Wireb/Cyphercon-5_3-2022/inkscape/coyote/coyote-F_SilkS_connect2.png

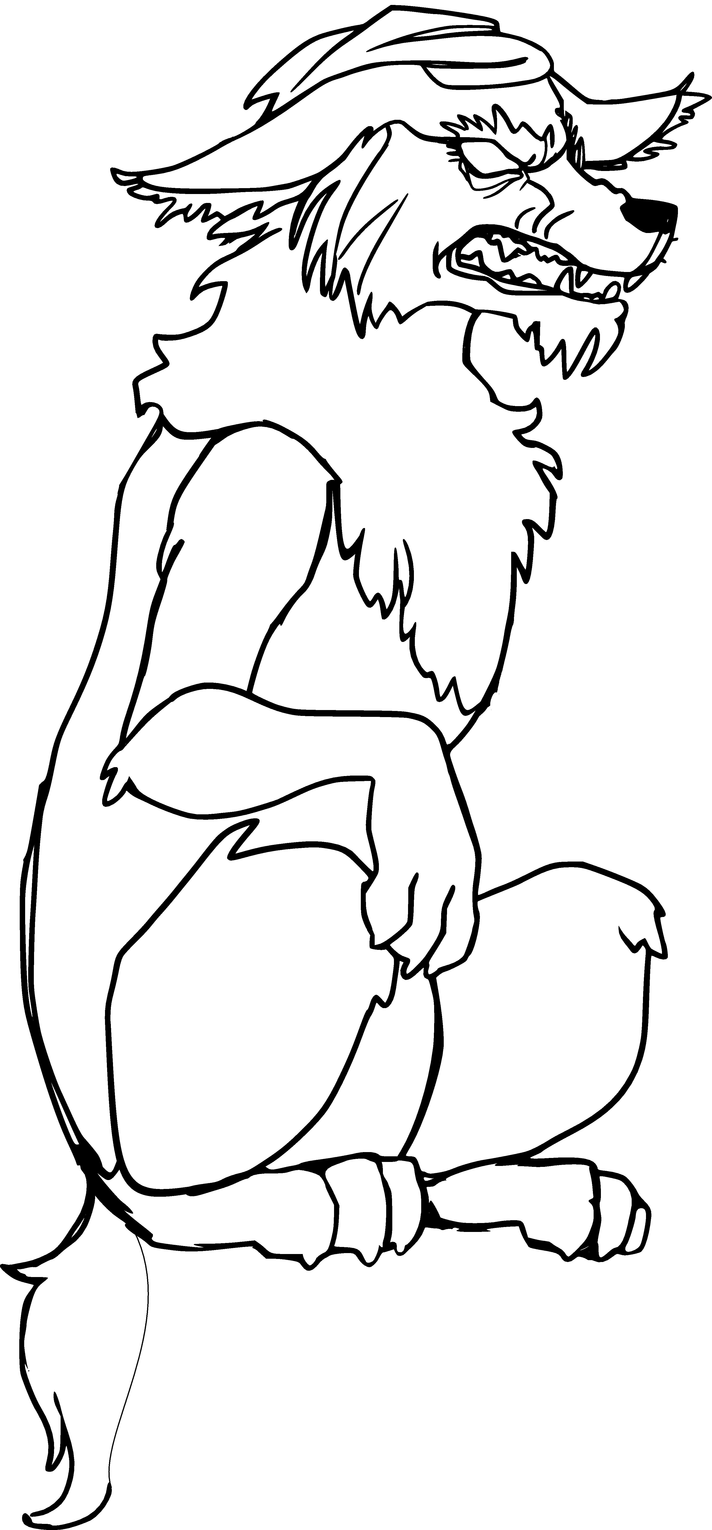
inkscape/coyote/coyote-F_SilkS_connect2.png
