Wireb/Cyphercon-5_3-2022/inkscape/Flamingo/2_tone_temp-F_SilkS_cleaned_thick.png

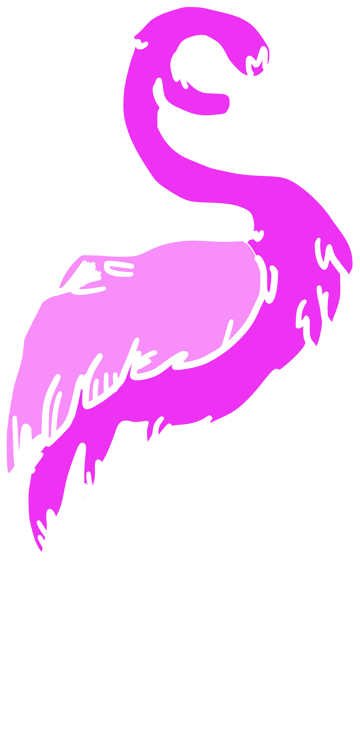
inkscape/Flamingo/2_tone_temp-F_SilkS_cleaned_thick.png
