Wireb/Cyphercon-5_3-2022/inkscape/Llama/llama-F_SilkS_hair.png

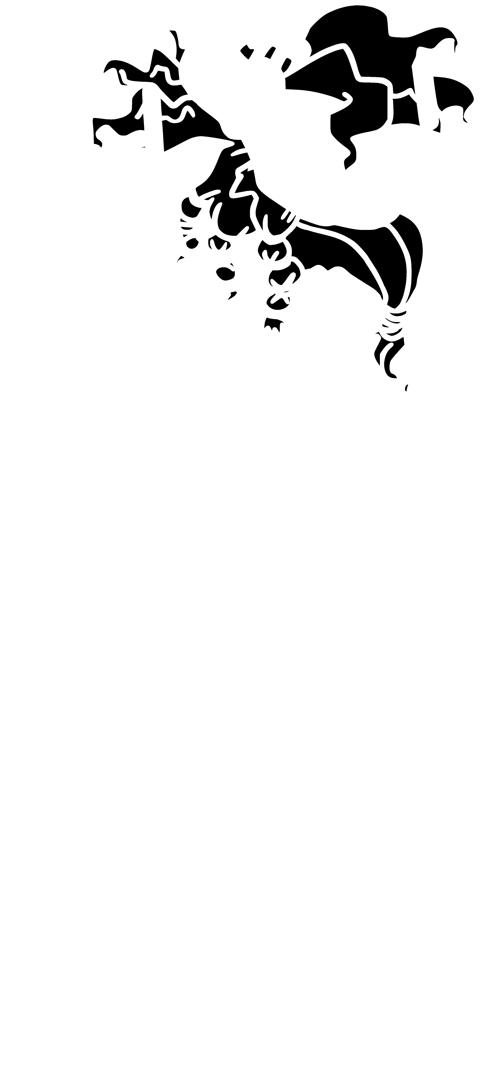
inkscape/Llama/llama-F_SilkS_hair.png
