Wireb/Cyphercon-5_3-2022/inkscape/Parrot/Parrot-F_SilkS.png

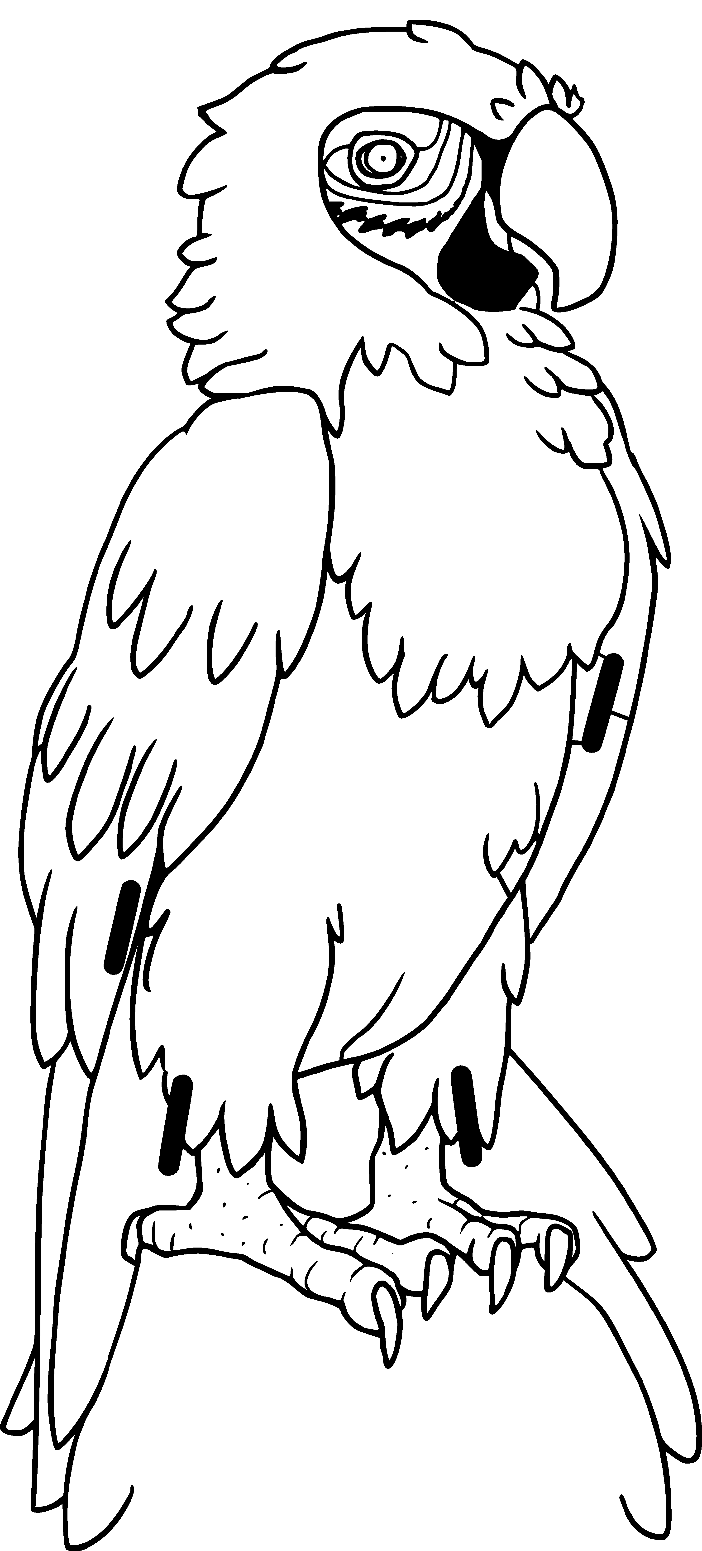
inkscape/Parrot/Parrot-F_SilkS.png
