Wireb/Cyphercon-5_3-2022/inkscape/Parrot/Parrot-F_SilkS_outline_inv.png

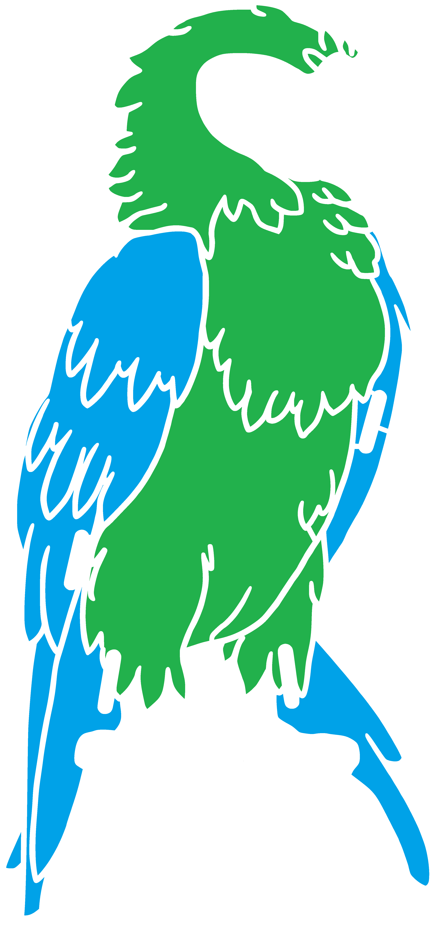
inkscape/Parrot/Parrot-F_SilkS_outline_inv.png
