Wireb/Cyphercon-5_3-2022/FreeCAD/tymkrs_Cyphercon_2020/wash_holder_base.stl

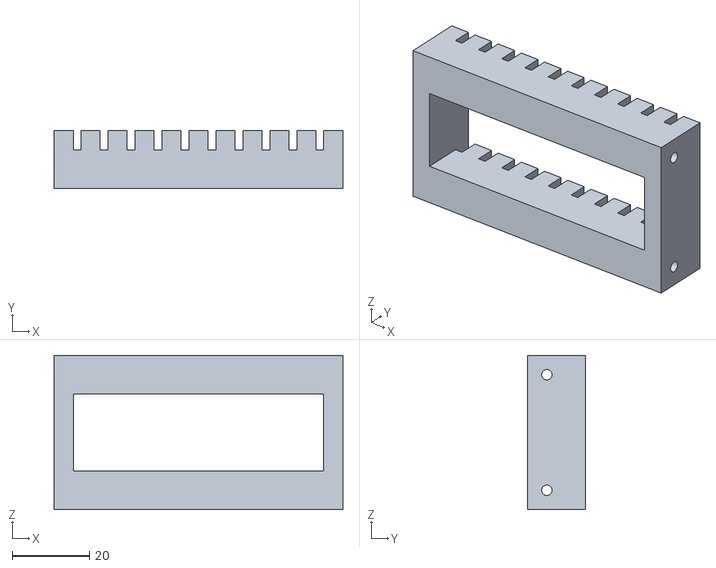
[picture p23: CAD file, 2022-05-03]
FreeCAD/tymkrs_Cyphercon_2020/wash_holder_base.stl
75.0 x 15.0 x 40.0
