Wireb/Cyphercon-5_3-2022/FreeCAD/Start button-2022/iris_arm (Meshed)001.stl

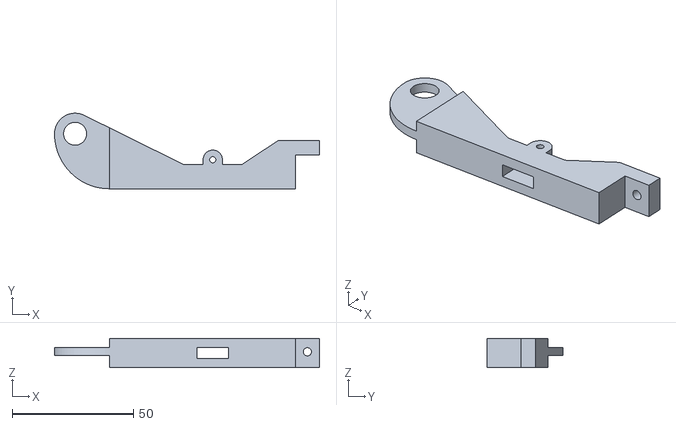
[picture p24: CAD file, 2022-05-03]
FreeCAD/Start button-2022/iris_arm (Meshed)001.stl
109.5 x 31.2 x 12.0
