Wireb/Cyphercon-5_3-2022/FreeCAD/tymkrs_Cyphercon_2020/bottle_button_support.FCStd

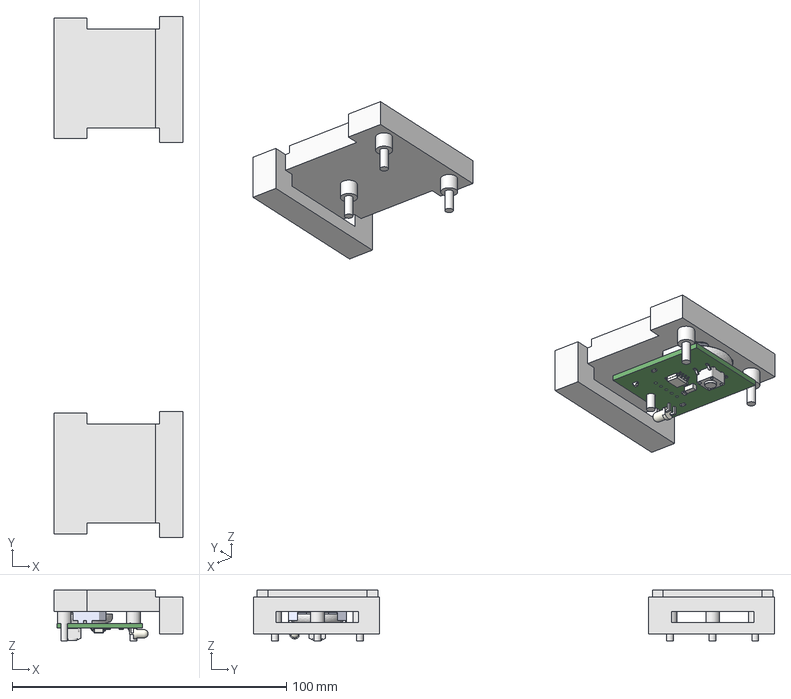
[picture p25: CAD file, 2022-05-03]
FreeCAD/tymkrs_Cyphercon_2020/bottle_button_support.FCStd
47.0 x 190.0 x 18.5 mm
button_carrier
button_carrier (Meshed)
