Wireb/Cyphercon-5_3-2022/FreeCAD/Start button-2022/1185 Massive Arcade Button 100mm.step

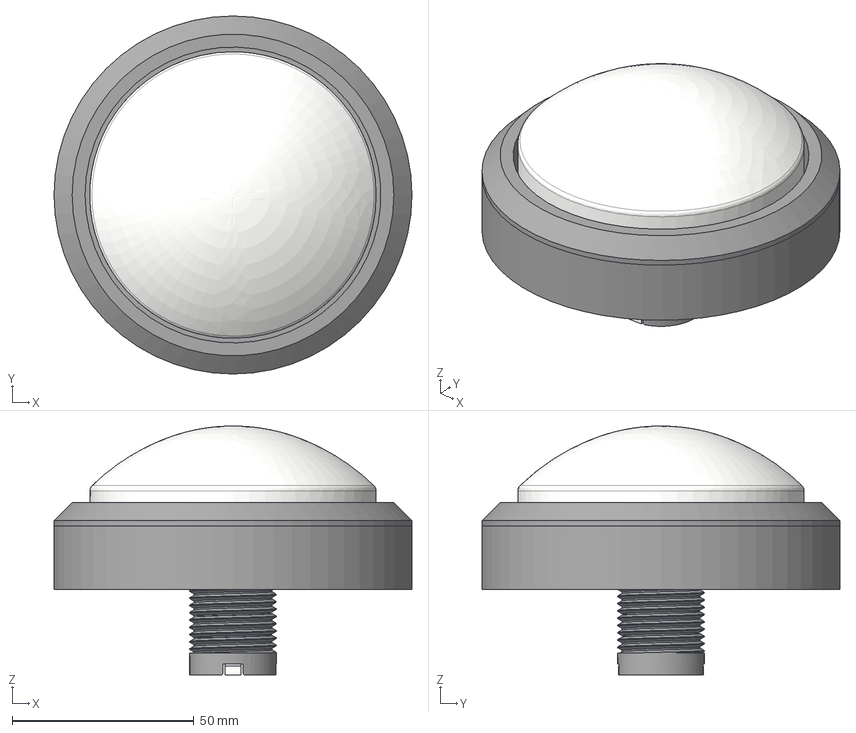
[picture p26: CAD file, 2022-05-03]
FreeCAD/Start button-2022/1185 Massive Arcade Button 100mm.step
98.5 x 98.5 x 68.5 mm
Base
Holder
Actuator
Spring
Dome
