Wireb/Cyphercon-5_3-2022/FreeCAD/tymkrs_Cyphercon_2020/Llama_top_flock (Meshed).stl

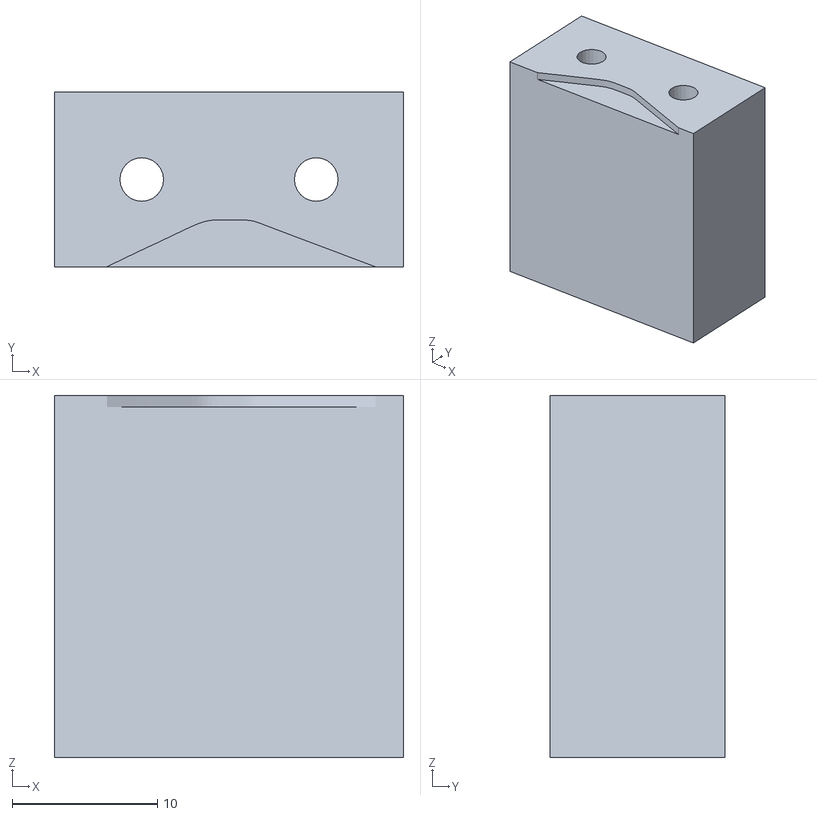
[picture p27: CAD file, 2022-05-03]
FreeCAD/tymkrs_Cyphercon_2020/Llama_top_flock (Meshed).stl
24.0 x 12.0 x 24.9
