Wireb/Cyphercon-5_3-2022/FreeCAD/Start button-2022/slider_plate (Meshed).stl

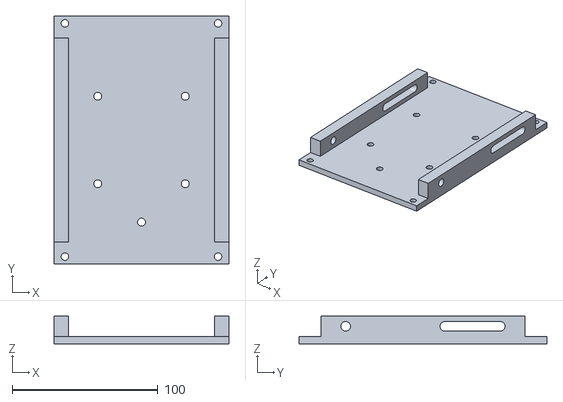
[picture p28: CAD file, 2022-05-03]
FreeCAD/Start button-2022/slider_plate (Meshed).stl
120.0 x 170.0 x 19.0
