Wireb/Cyphercon-5_3-2022/FreeCAD/tymkrs_Cyphercon_2020/Destaco_604.stp

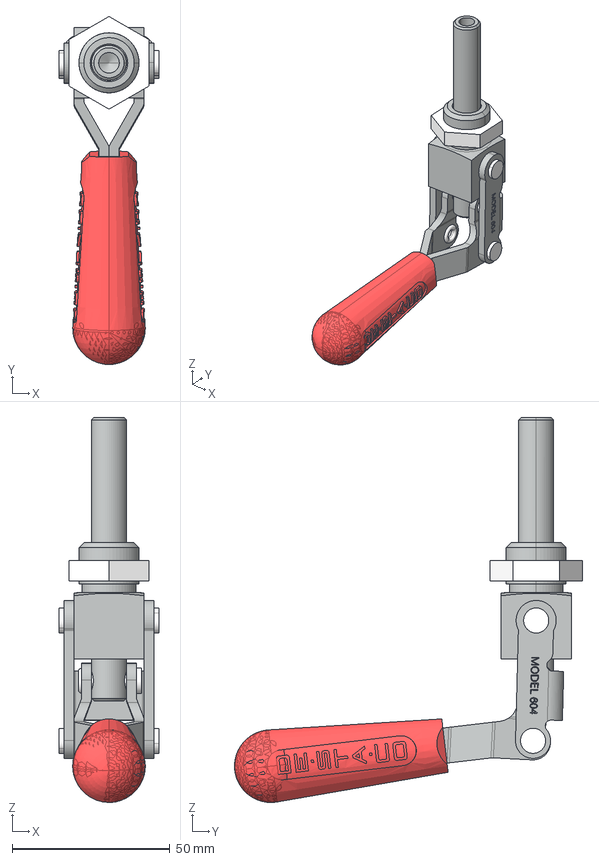
[picture p30: CAD file, 2022-05-03]
FreeCAD/tymkrs_Cyphercon_2020/Destaco_604.stp
31.7 x 110.2 x 121.9 mm
MSBR-2604_
MSBR-1604_
604_PLUNGER
604_BODY_2
604_BODY_3
604_BODY_1
604_BODY_10
MSBR-5604_
MSBR-4604_
MSBR-3604_ x 3
