Wireb/Cyphercon-5_3-2022/FreeCAD/Start button-2022/Petal (Meshed).stl

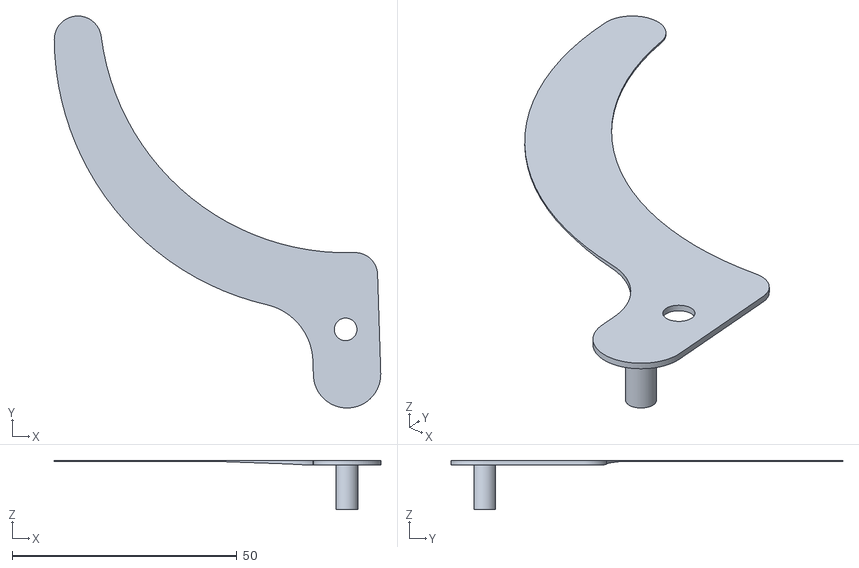
[picture p31: CAD file, 2022-05-03]
FreeCAD/Start button-2022/Petal (Meshed).stl
72.6 x 87.2 x 11.0
