Wireb/Cyphercon-5_3-2022/FreeCAD/tymkrs_Cyphercon_2020/Parrot_wings_stencil (Meshed).3mf

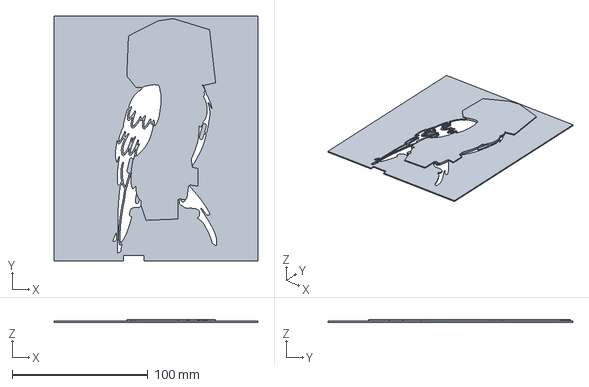
[picture p32: CAD file, 2022-05-03]
FreeCAD/tymkrs_Cyphercon_2020/Parrot_wings_stencil (Meshed).3mf
150.0 x 180.0 x 2.00 mm
