Wireb/Cyphercon-5_3-2022/FreeCAD/Start button-2022/button_plate (Meshed).stl

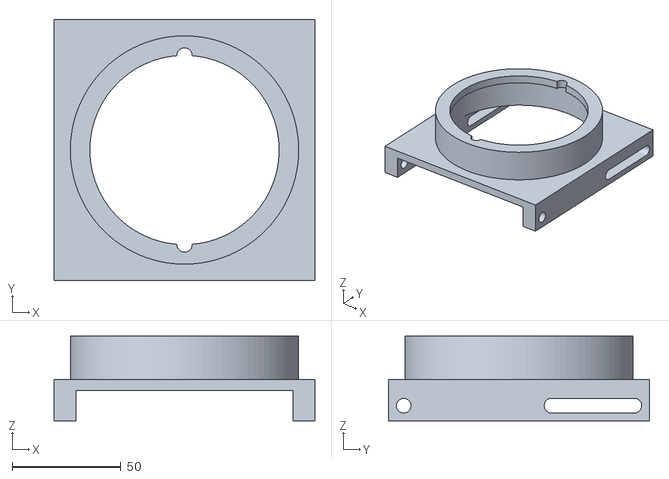
[picture p33: CAD file, 2022-05-03]
FreeCAD/Start button-2022/button_plate (Meshed).stl
120.0 x 120.0 x 39.0
