Wireb/Cyphercon-5_3-2022/FreeCAD/tymkrs_Cyphercon_2020/Starfish.FCStd

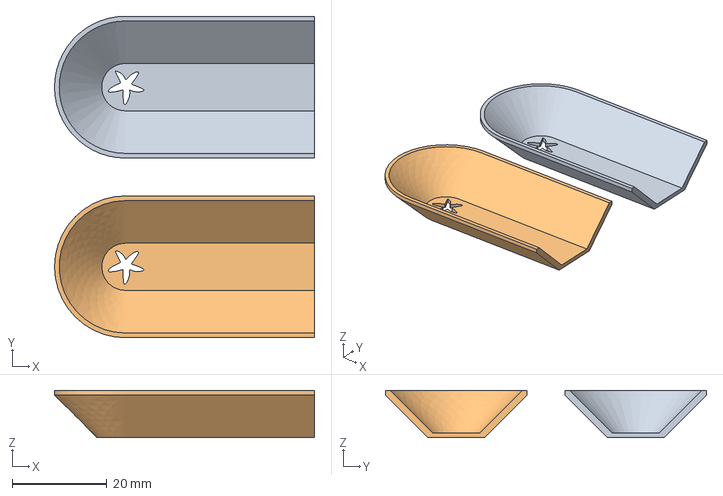
[picture p34: CAD file, 2022-05-03]
FreeCAD/tymkrs_Cyphercon_2020/Starfish.FCStd
55.0 x 68.0 x 10.0 mm
Cut001 (Meshed)
