Wireb/Cyphercon-5_3-2022/FreeCAD/Start button-2022/Lift pully (Meshed).stl

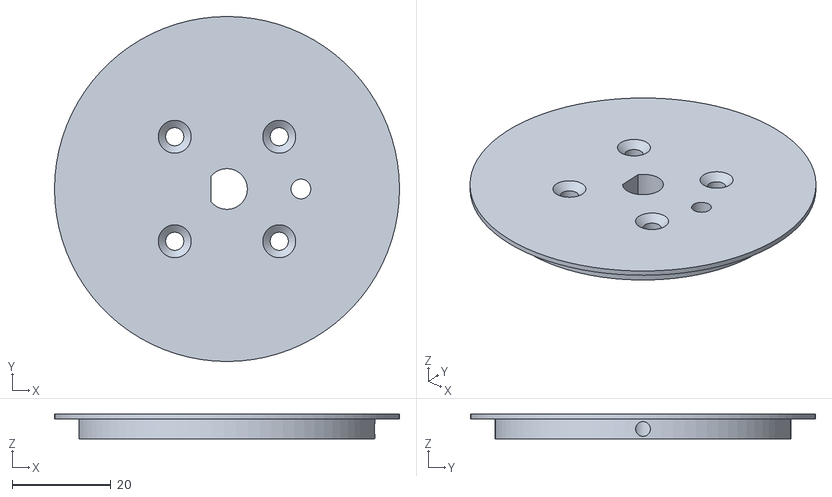
[picture p35: CAD file, 2022-05-03]
FreeCAD/Start button-2022/Lift pully (Meshed).stl
70.0 x 70.0 x 5.00
