Wireb/Cyphercon-5_3-2022/FreeCAD/tymkrs_Cyphercon_2020/Llama_bottom_flock (Meshed).stl

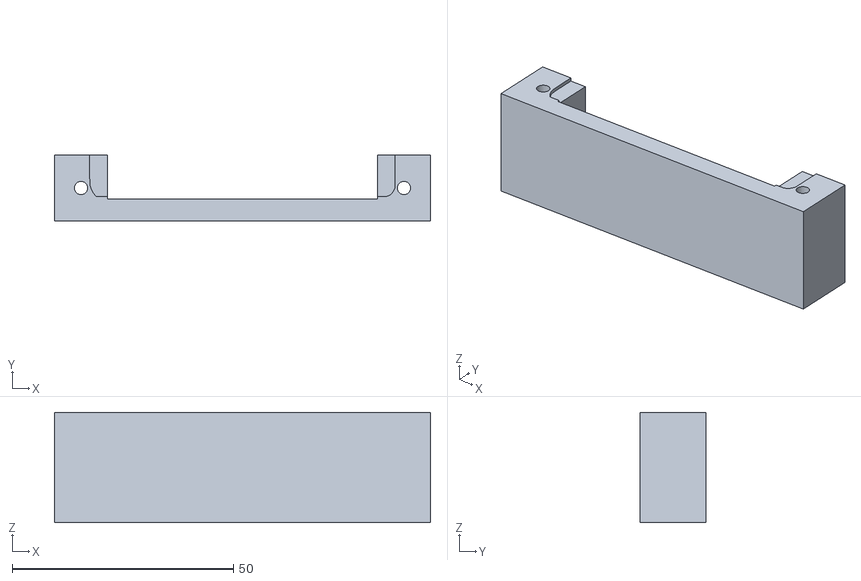
[picture p36: CAD file, 2022-05-03]
FreeCAD/tymkrs_Cyphercon_2020/Llama_bottom_flock (Meshed).stl
85.0 x 15.0 x 24.9
