Wireb/Cyphercon-5_3-2022/FreeCAD/Start button-2022/start button_V1.FCStd

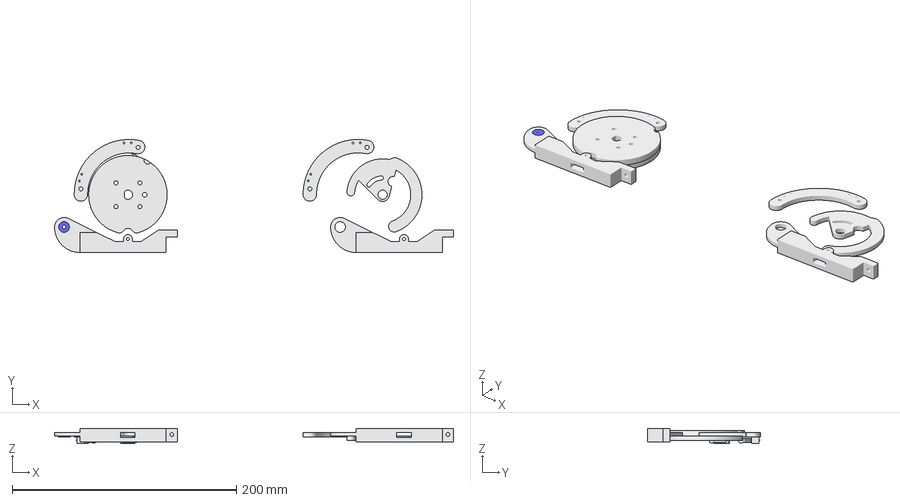
[picture p37: CAD file, 2022-05-03]
FreeCAD/Start button-2022/start button_V1.FCStd
355.5 x 100.7 x 13.6 mm
SSR-2ZZ bearings
iris_arm
Cam_disk
Switch_bracket
D2F_L2_D_BASE
D2F_L2_D_ACTUATOR
D2F_L2_D_BASE001
D2F_L2_D_ACTUATOR001
Switch_cam
Switch_bracket (Meshed)
iris_arm (Meshed)
Switch_cam (Meshed)
