Wireb/Cyphercon-5_3-2022/FreeCAD/Start button-2022/Switch_cam (Meshed).stl

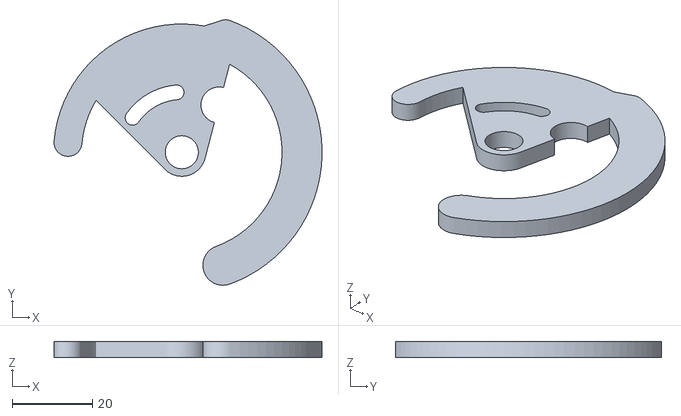
[picture p38: CAD file, 2022-05-03]
FreeCAD/Start button-2022/Switch_cam (Meshed).stl
66.9 x 66.3 x 4.00
