Wireb/Cyphercon-5_3-2022/FreeCAD/tymkrs_Cyphercon_2020/button_case.FCStd

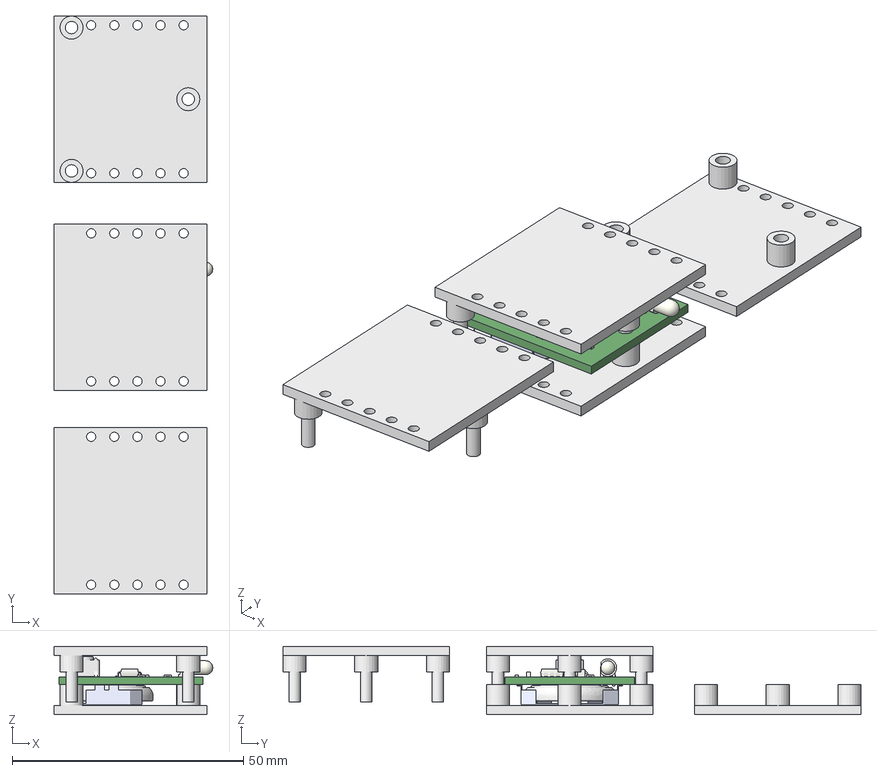
[picture p39: CAD file, 2022-05-03]
FreeCAD/tymkrs_Cyphercon_2020/button_case.FCStd
34.3 x 125.0 x 14.8 mm
top_case
bottom_case
top_case (Meshed)
bottom_case (Meshed)
