Wireb/Cyphercon-5_3-2022/FreeCAD/Start button-2022/D2F_L2_D.step

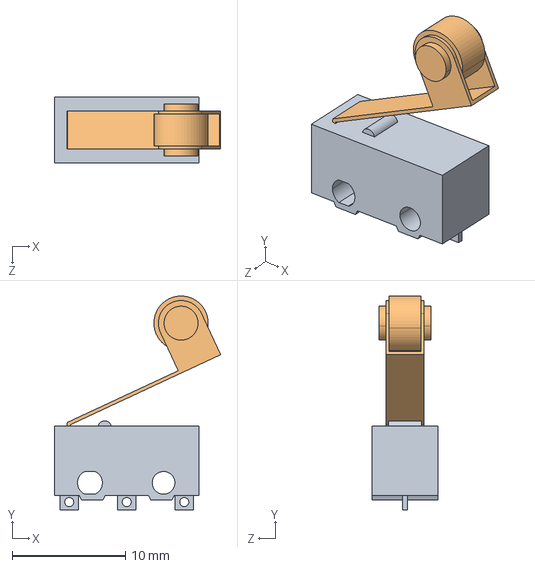
[picture p40: CAD file, 2022-05-03]
FreeCAD/Start button-2022/D2F_L2_D.step
14.7 x 18.9 x 5.80 mm
D2F_L2_D_BASE
D2F_L2_D_ACTUATOR
