Wireb/Cyphercon-5_3-2022/FreeCAD/tymkrs_Cyphercon_2020/Cut (Meshed).stl

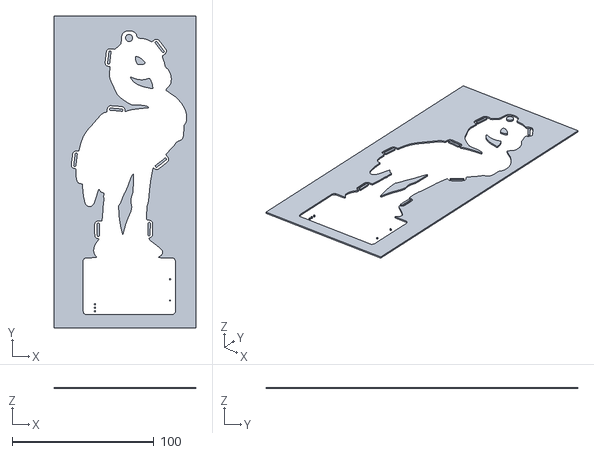
[picture p41: CAD file, 2022-05-03]
FreeCAD/tymkrs_Cyphercon_2020/Cut (Meshed).stl
100.0 x 220.0 x 1.00
