Wireb/Cyphercon-5_3-2022/FreeCAD/Start button-2022/Cam_disk (Meshed).stl

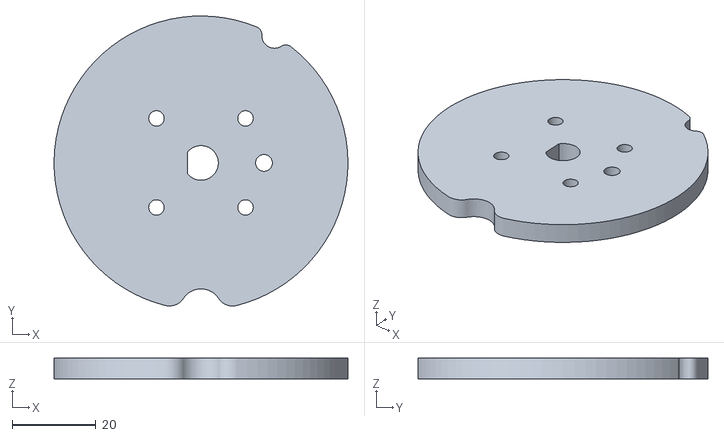
[picture p42: CAD file, 2022-05-03]
FreeCAD/Start button-2022/Cam_disk (Meshed).stl
70.0 x 69.1 x 4.95
