Wireb/Cyphercon-5_3-2022/FreeCAD/tymkrs_Cyphercon_2020/Nest flamingo pgm(Meshed).stl

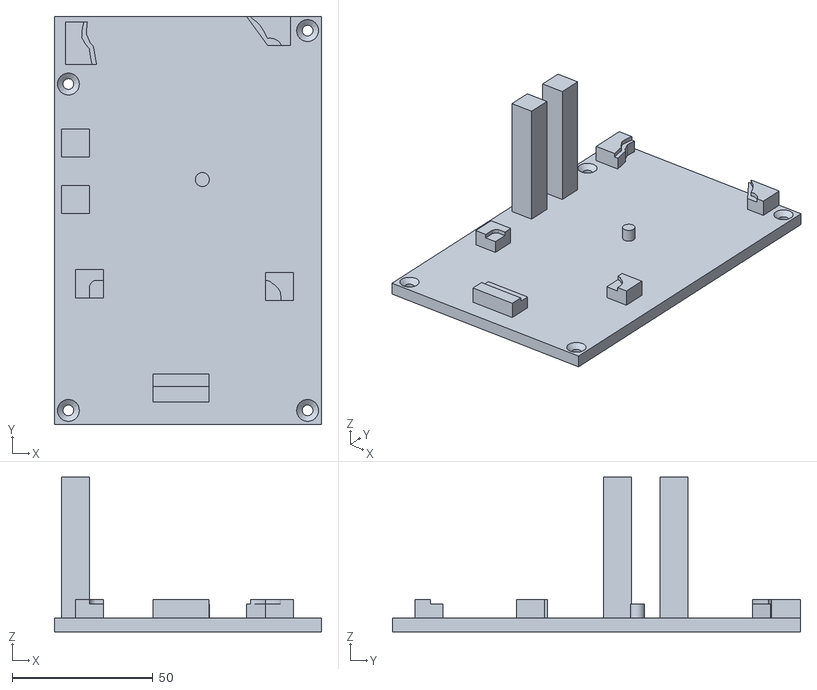
[picture p43: CAD file, 2022-05-03]
FreeCAD/tymkrs_Cyphercon_2020/Nest flamingo pgm(Meshed).stl
95.0 x 145.0 x 55.0
