Wireb/Cyphercon-5_3-2022/FreeCAD/Start button-2022/Petal (Meshed) v0.stl

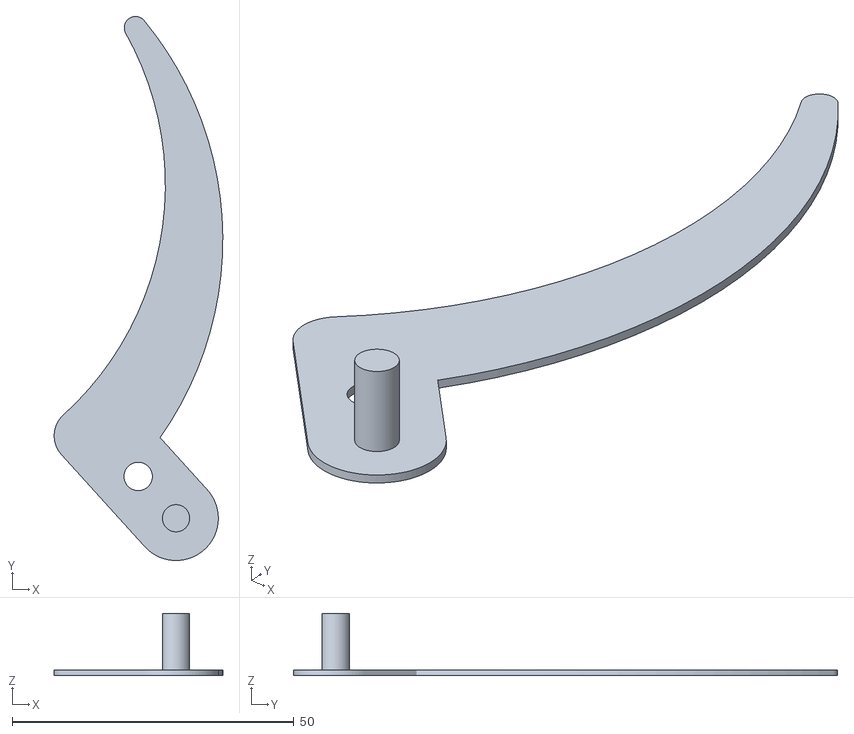
[picture p44: CAD file, 2022-05-03]
FreeCAD/Start button-2022/Petal (Meshed) v0.stl
29.9 x 96.5 x 11.0
