Wireb/Cyphercon-5_3-2022/FreeCAD/tymkrs_Cyphercon_2020/flamingo_final (Meshed).stl

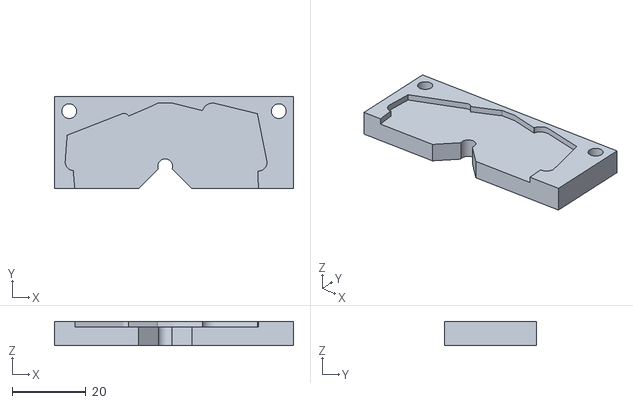
[picture p45: CAD file, 2022-05-03]
FreeCAD/tymkrs_Cyphercon_2020/flamingo_final (Meshed).stl
65.0 x 25.1 x 6.60
