Wireb/Cyphercon-5_3-2022/FreeCAD/Start button-2022/Switch_bracket (Meshed).stl

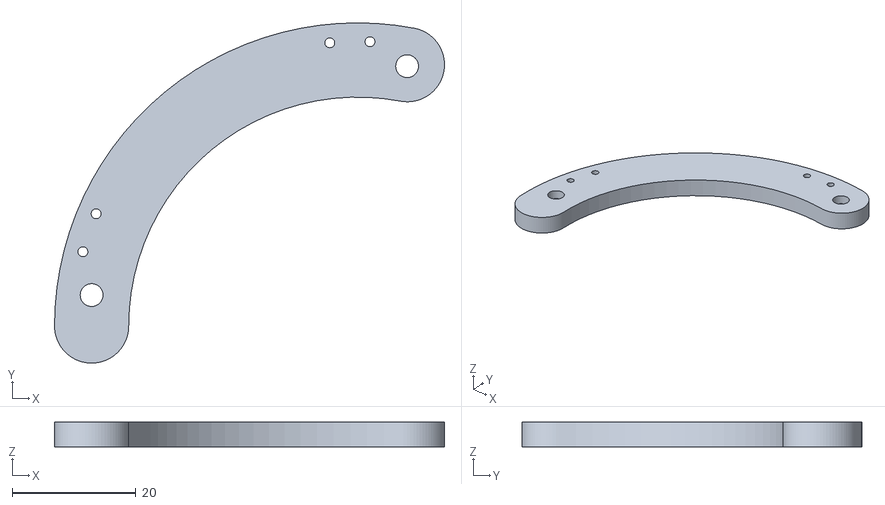
[picture p46: CAD file, 2022-05-03]
FreeCAD/Start button-2022/Switch_bracket (Meshed).stl
63.0 x 55.0 x 4.00
