Wireb/Cyphercon-5_3-2022/FreeCAD/Start button-2022/Key_sw_spacer (Meshed).stl

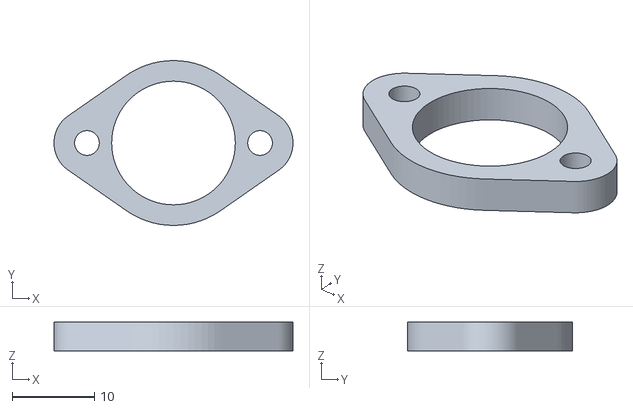
[picture p47: CAD file, 2022-05-03]
FreeCAD/Start button-2022/Key_sw_spacer (Meshed).stl
29.0 x 20.0 x 3.50
