Wireb/Cyphercon-5_3-2022/FreeCAD/tymkrs_Cyphercon_2020/Outhouse_socket (Meshed).stl

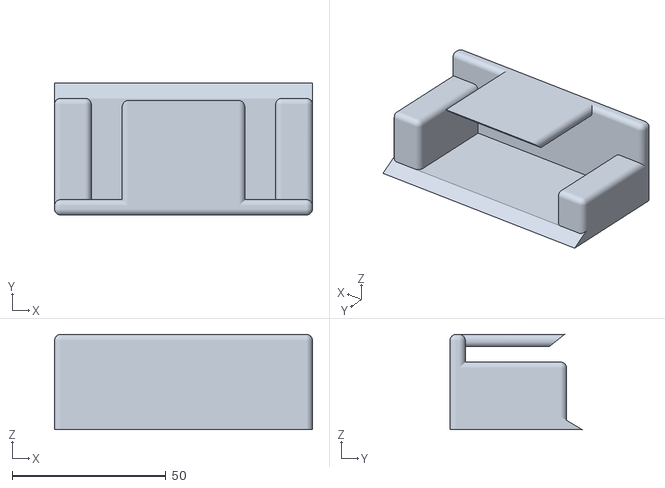
[picture p48: CAD file, 2022-05-03]
FreeCAD/tymkrs_Cyphercon_2020/Outhouse_socket (Meshed).stl
84.0 x 43.0 x 31.0
