Wireb/Cyphercon-5_3-2022/FreeCAD/tymkrs_Cyphercon_2020/coyote_stencil (Meshed).stl

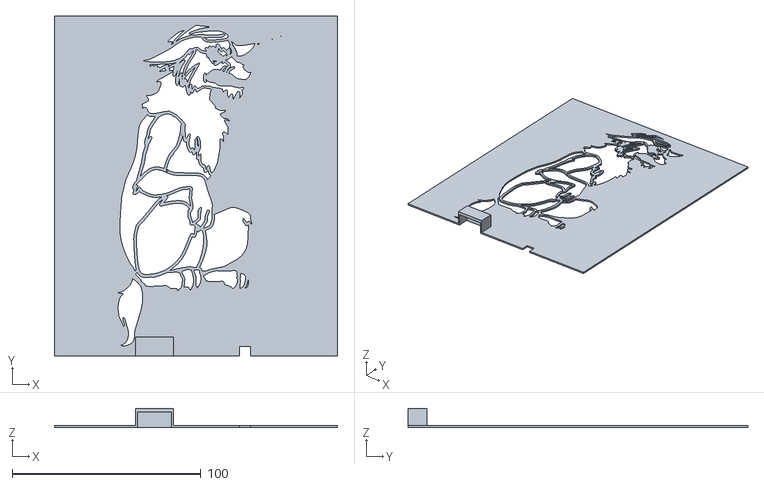
[picture p49: CAD file, 2022-05-03]
FreeCAD/tymkrs_Cyphercon_2020/coyote_stencil (Meshed).stl
150.0 x 180.0 x 10.2
