Wireb/Cyphercon-5_3-2022/FreeCAD/Start button-2022/start button.FCStd

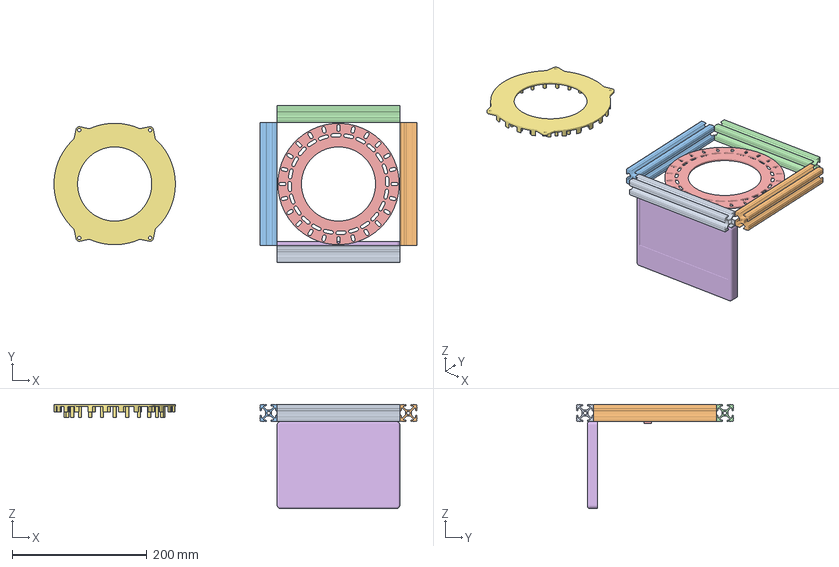
[picture p50: CAD file, 2022-05-03]
FreeCAD/Start button-2022/start button.FCStd
538.4 x 232.8 x 154.4 mm
1" extrusion horisontal001
1" extrusion horisontal002
1" extrusion horisontal004
1" extrusion horisontal006
Top Ring
LED panel001
Mounting ring (Meshed)
