Wireb/Cyphercon-5_3-2022/FreeCAD/Start button-2022/Top Ring (Meshed).stl

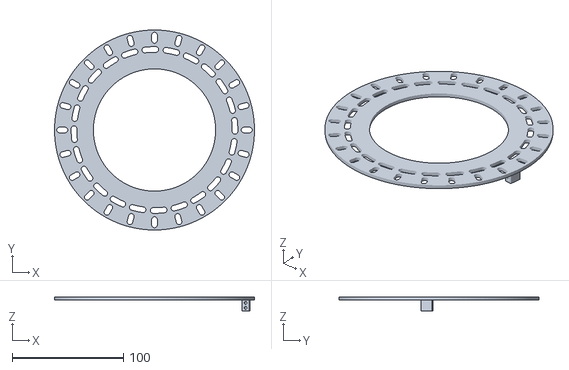
[picture p51: CAD file, 2022-05-03]
FreeCAD/Start button-2022/Top Ring (Meshed).stl
180.0 x 180.0 x 13.0
