Wireb/Cyphercon-5_3-2022/FreeCAD/tymkrs_Cyphercon_2020/flamingo stencil(Meshed).stl

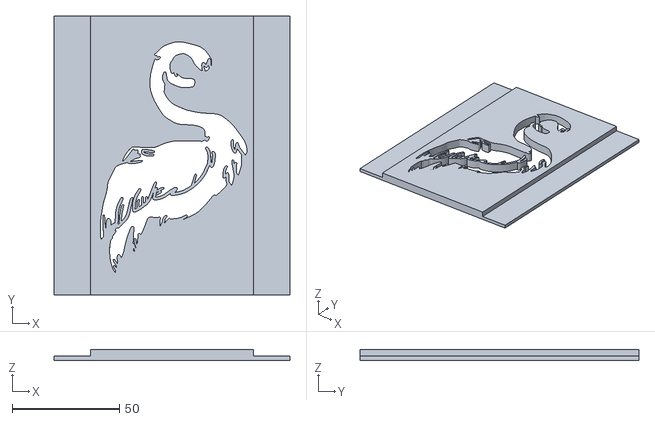
[picture p52: CAD file, 2022-05-03]
FreeCAD/tymkrs_Cyphercon_2020/flamingo stencil(Meshed).stl
110.0 x 130.0 x 5.00
