Wireb/Cyphercon-5_3-2022/FreeCAD/tymkrs_Cyphercon_2020/coyote_final (Meshed).stl

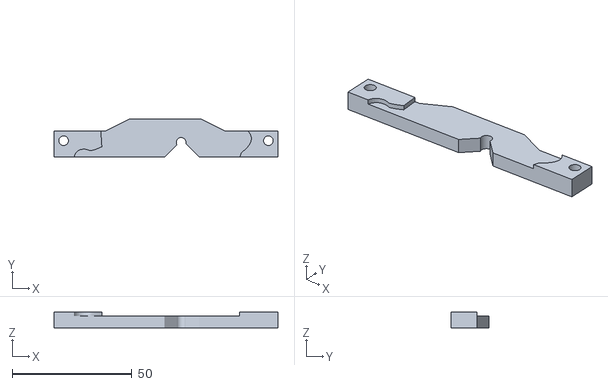
[picture p54: CAD file, 2022-05-03]
FreeCAD/tymkrs_Cyphercon_2020/coyote_final (Meshed).stl
93.4 x 15.8 x 6.60
