Wireb/Cyphercon-5_3-2022/FreeCAD/tymkrs_Cyphercon_2020/SS_01GL_E.step

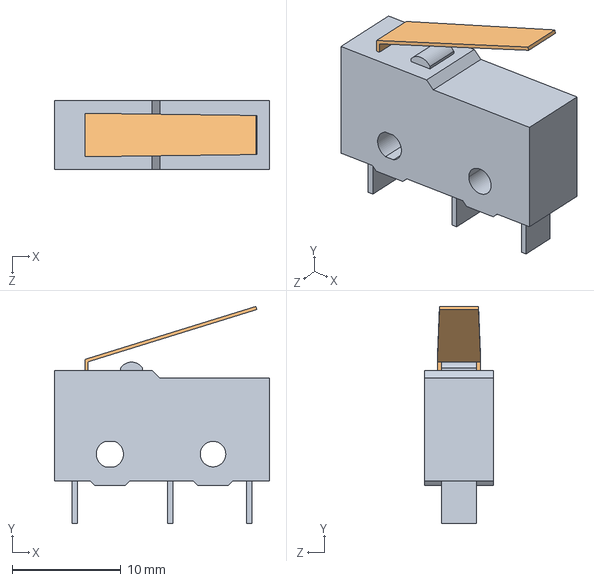
[picture p55: CAD file, 2022-05-03]
FreeCAD/tymkrs_Cyphercon_2020/SS_01GL_E.step
19.8 x 20.0 x 6.40 mm
SS_01GL_E_BASE
SS_01GL_E_ACTUATOR
