Wireb/Cyphercon-5_3-2022/FreeCAD/tymkrs_Cyphercon_2020/wash_holders.FCStd

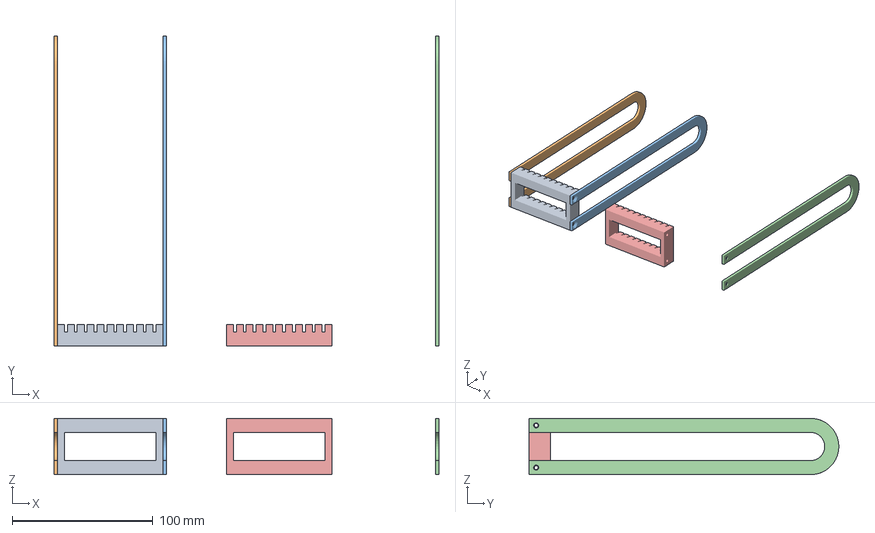
[picture p56: CAD file, 2022-05-03]
FreeCAD/tymkrs_Cyphercon_2020/wash_holders.FCStd
273.5 x 220.0 x 40.0 mm
Body001 (Meshed)
Body (Meshed)
