Wireb/Cyphercon-5_3-2022/FreeCAD/tymkrs_Cyphercon_2020/parrot_flock_blocks.3mf

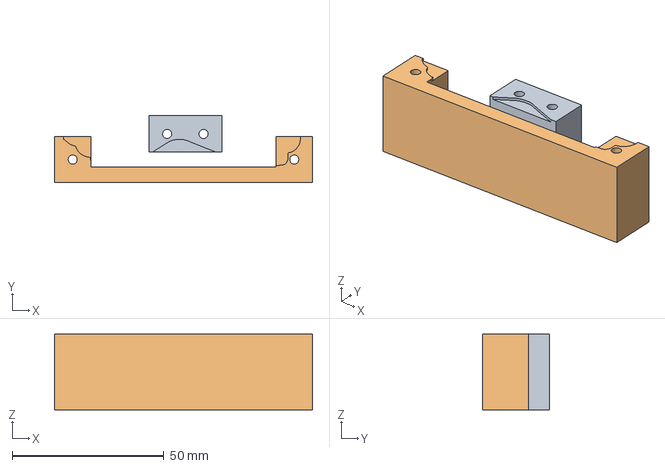
[picture p57: CAD file, 2022-05-03]
FreeCAD/tymkrs_Cyphercon_2020/parrot_flock_blocks.3mf
85.0 x 21.9 x 24.9 mm
parrot_top_flock_block (Meshed).stl
parrot_bottom_flock_block (Meshed).stl
