Wireb/Cyphercon-5_3-2022/FreeCAD/tymkrs_Cyphercon_2020/flamingo_wing_stencil.3mf

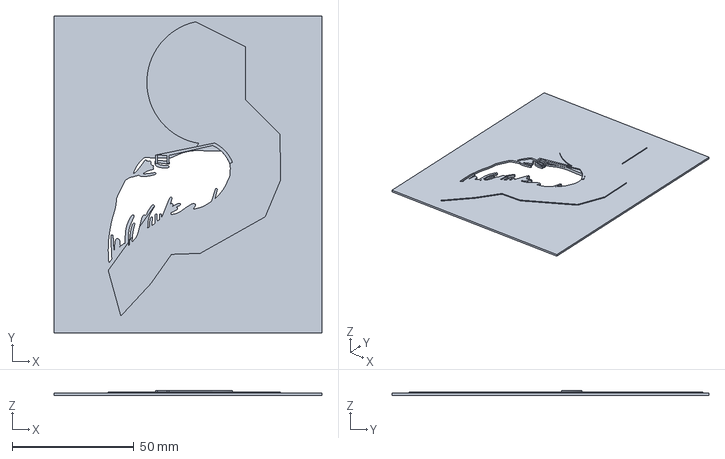
[picture p58: CAD file, 2022-05-03]
FreeCAD/tymkrs_Cyphercon_2020/flamingo_wing_stencil.3mf
110.0 x 130.0 x 2.00 mm
