Wireb/Cyphercon-5_3-2022/FreeCAD/tymkrs_Cyphercon_2020/screen_alignment_jig.stl

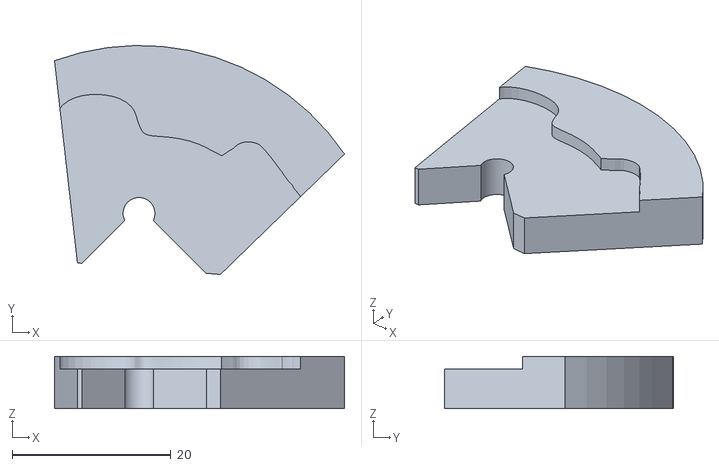
[picture p59: CAD file, 2022-05-03]
FreeCAD/tymkrs_Cyphercon_2020/screen_alignment_jig.stl
36.5 x 28.8 x 6.60
