Wireb/Cyphercon-5_3-2022/FreeCAD/tymkrs_Cyphercon_2020/top cover (Meshed).stl

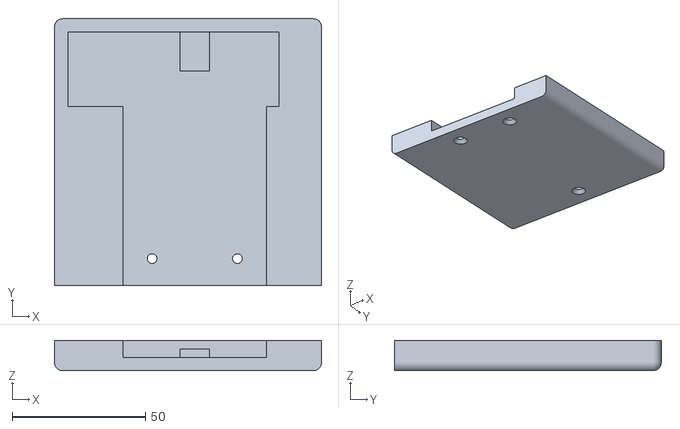
[picture p60: CAD file, 2022-05-03]
FreeCAD/tymkrs_Cyphercon_2020/top cover (Meshed).stl
100.2 x 100.0 x 11.3
