Wireb/Cyphercon-5_3-2022/FreeCAD/tymkrs_Cyphercon_2020/port a poty back (Meshed).3mf

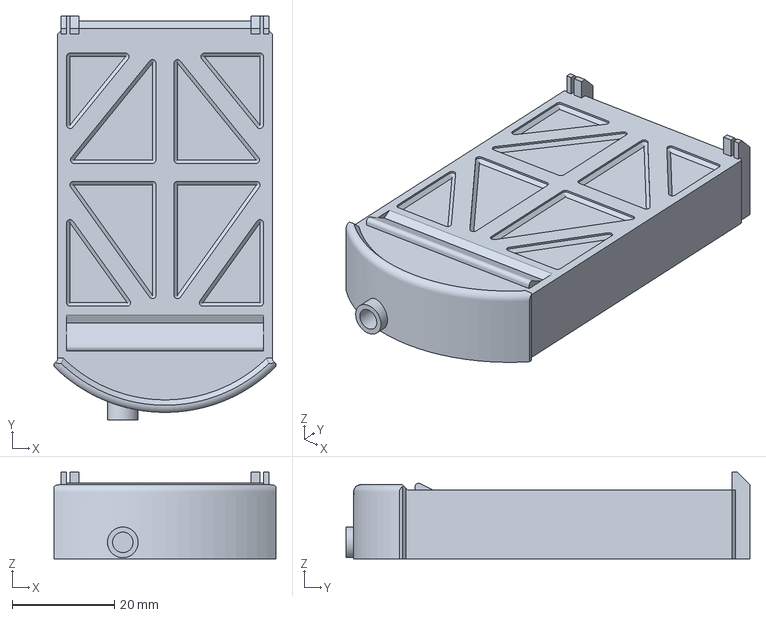
[picture p61: CAD file, 2022-05-03]
FreeCAD/tymkrs_Cyphercon_2020/port a poty back (Meshed).3mf
43.4 x 79.0 x 17.0 mm
