Wireb/Cyphercon-5_3-2022/FreeCAD/tymkrs_Cyphercon_2020/Wash_holder_handle.stl

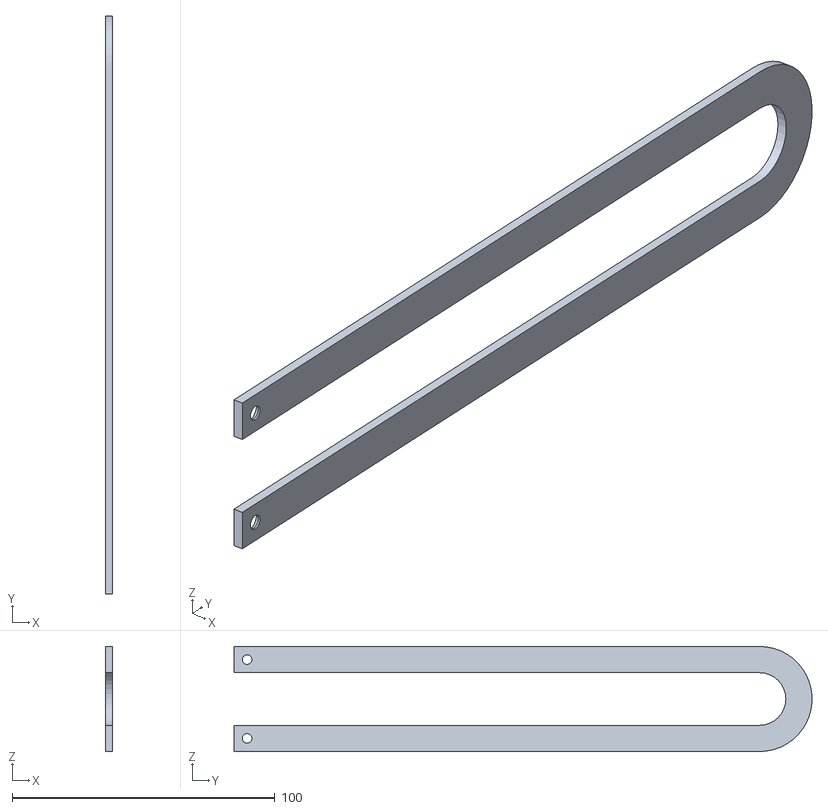
[picture p62: CAD file, 2022-05-03]
FreeCAD/tymkrs_Cyphercon_2020/Wash_holder_handle.stl
2.50 x 220.0 x 40.0
