Wireb/Cyphercon-5_3-2022/FreeCAD/tymkrs_Cyphercon_2020/bottom_case (Meshed).stl

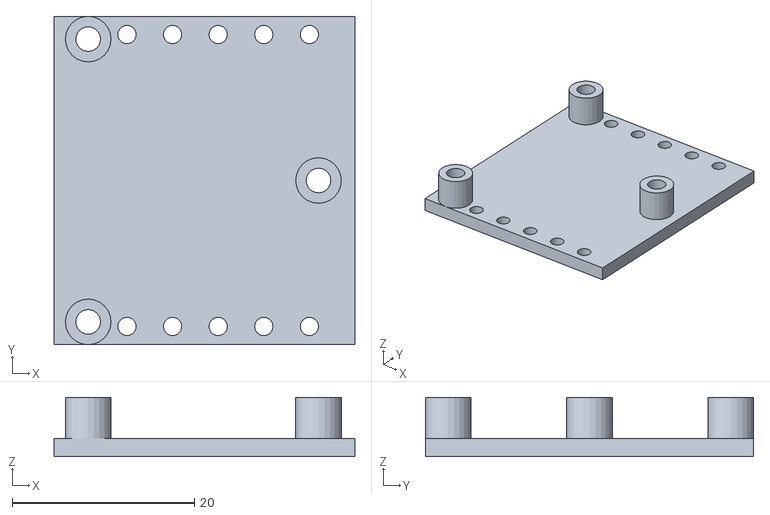
[picture p63: CAD file, 2022-05-03]
FreeCAD/tymkrs_Cyphercon_2020/bottom_case (Meshed).stl
33.0 x 36.0 x 6.50
