Wireb/Cyphercon-5_3-2022/FreeCAD/tymkrs_Cyphercon_2020/bar alignment (Meshed).stl

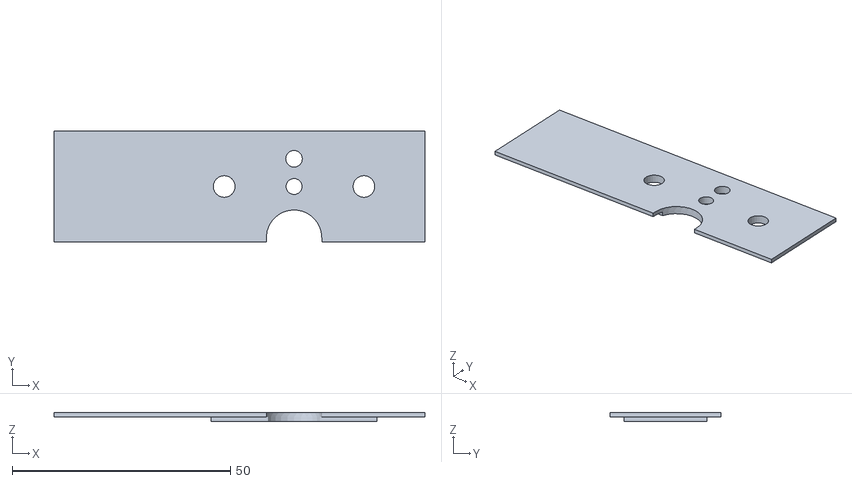
[picture p64: CAD file, 2022-05-03]
FreeCAD/tymkrs_Cyphercon_2020/bar alignment (Meshed).stl
85.0 x 25.4 x 2.00
