Wireb/Cyphercon-5_3-2022/FreeCAD/tymkrs_Cyphercon_2020/Test_probe_hole (Meshed).stl

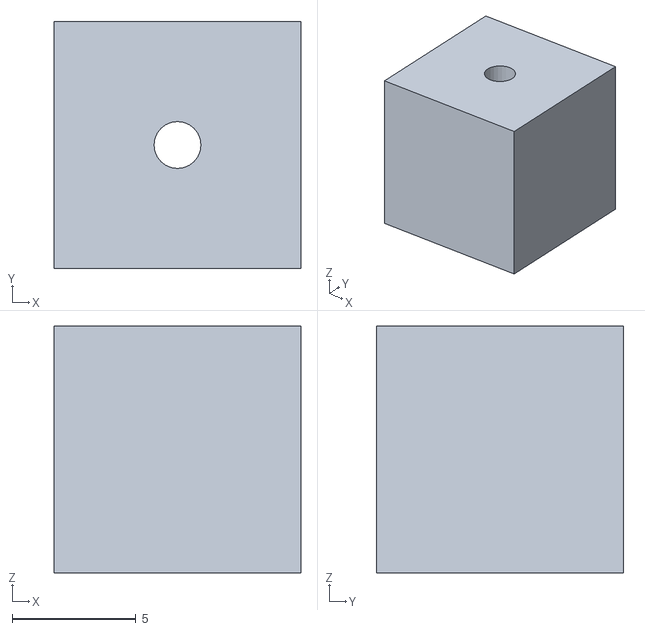
[picture p65: CAD file, 2022-05-03]
FreeCAD/tymkrs_Cyphercon_2020/Test_probe_hole (Meshed).stl
10.0 x 10.0 x 10.0
