Wireb/Cyphercon-5_3-2022/FreeCAD/tymkrs_Cyphercon_2020/Vendo_bracket.FCStd

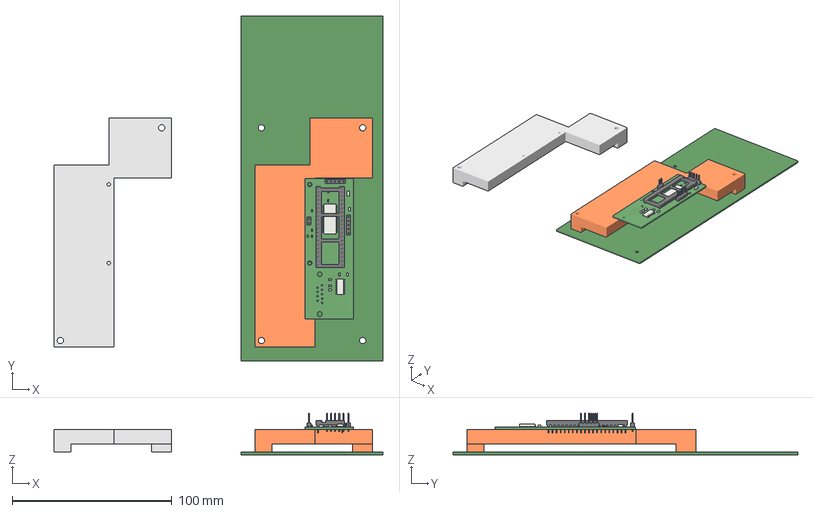
[picture p66: CAD file, 2022-05-03]
FreeCAD/tymkrs_Cyphercon_2020/Vendo_bracket.FCStd
206.2 x 216.0 x 26.0 mm
main PCB
Bracket
Bracket (Meshed)
