Wireb/Cyphercon-5_3-2022/FreeCAD/tymkrs_Cyphercon_2020/flamingo_flock_blocks.FCStd

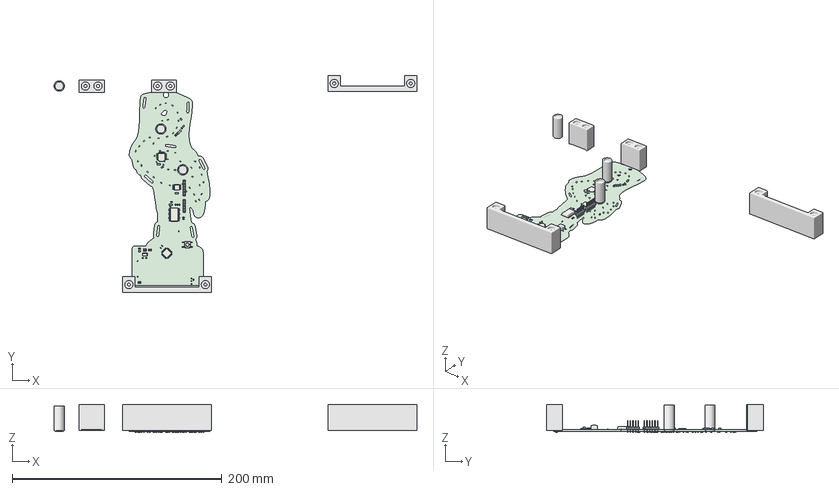
[picture p67: CAD file, 2022-05-03]
FreeCAD/tymkrs_Cyphercon_2020/flamingo_flock_blocks.FCStd
346.5 x 207.0 x 27.1 mm
center_support
Flamingo_flock_bottom_support
Flamingo_flock_top_support
center_support (Meshed)
Flamingo_flock_bottom_support (Meshed)
Flamingo_flock_top_support (Meshed)
center_support (Meshed)001
