Wireb/Cyphercon-5_3-2022/FreeCAD/tymkrs_Cyphercon_2020/Llama_body_stencil (Meshed).stl

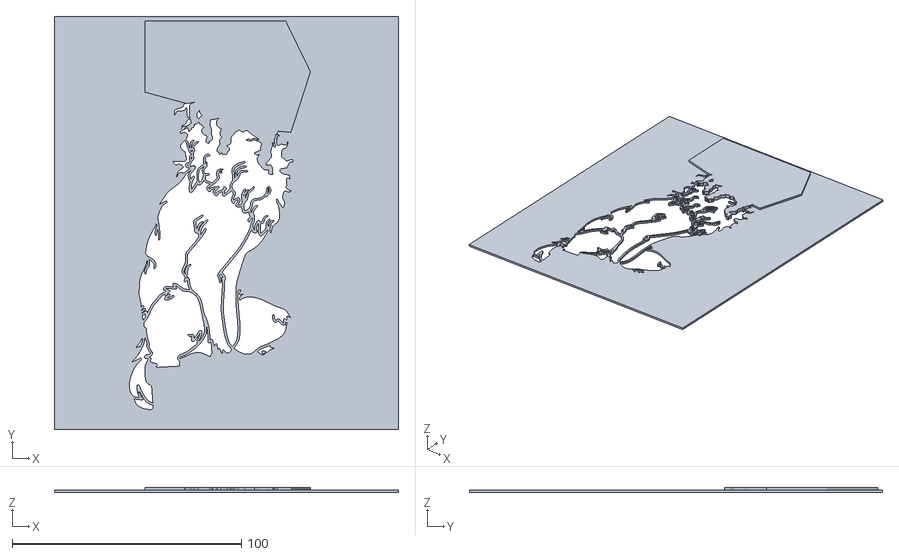
[picture p68: CAD file, 2022-05-03]
FreeCAD/tymkrs_Cyphercon_2020/Llama_body_stencil (Meshed).stl
150.0 x 180.0 x 2.00
