Wireb/Cyphercon-5_3-2022/FreeCAD/tymkrs_Cyphercon_2020/llama_final(Meshed).stl

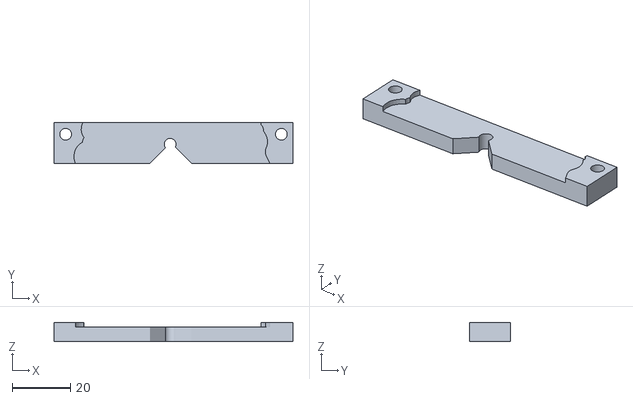
[picture p69: CAD file, 2022-05-03]
FreeCAD/tymkrs_Cyphercon_2020/llama_final(Meshed).stl
82.0 x 14.0 x 6.60
