Wireb/Cyphercon-5_3-2022/FreeCAD/tymkrs_Cyphercon_2020/center_support_flamingo (Meshed).3mf

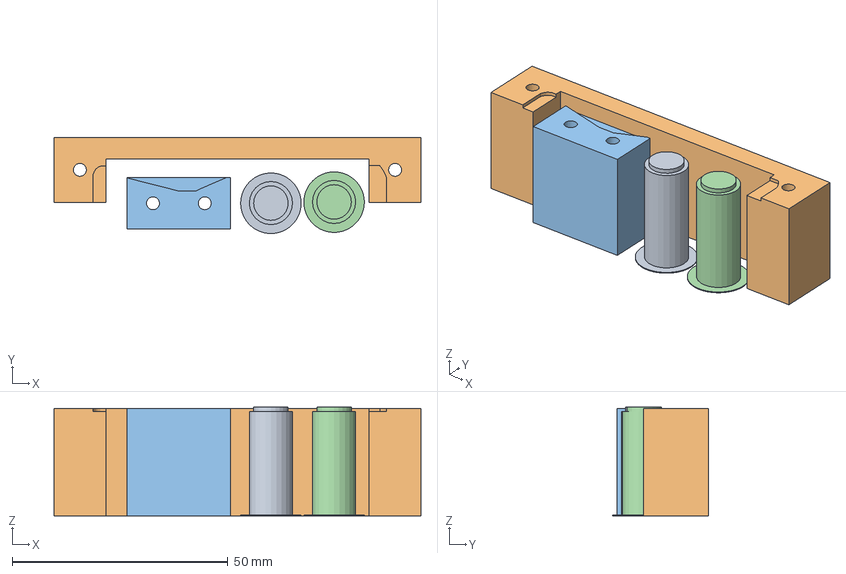
[picture p70: CAD file, 2022-05-03]
FreeCAD/tymkrs_Cyphercon_2020/center_support_flamingo (Meshed).3mf
85.0 x 22.2 x 25.2 mm
center_support_flamingo (Meshed).stl x 2
Flamingo_flock_bottom_support (Meshed).stl
Flamingo_flock_top_support (Meshed).stl
