Wireb/Cyphercon-5_3-2022/FreeCAD/tymkrs_Cyphercon_2020/button_carrier (Meshed).stl

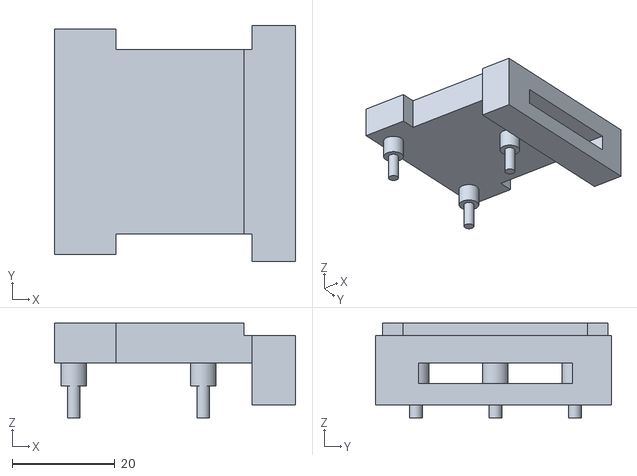
[picture p71: CAD file, 2022-05-03]
FreeCAD/tymkrs_Cyphercon_2020/button_carrier (Meshed).stl
47.0 x 46.0 x 18.5
