Wireb/Cyphercon-5_3-2022/FreeCAD/tymkrs_Cyphercon_2020/Holder front (Meshed).stl

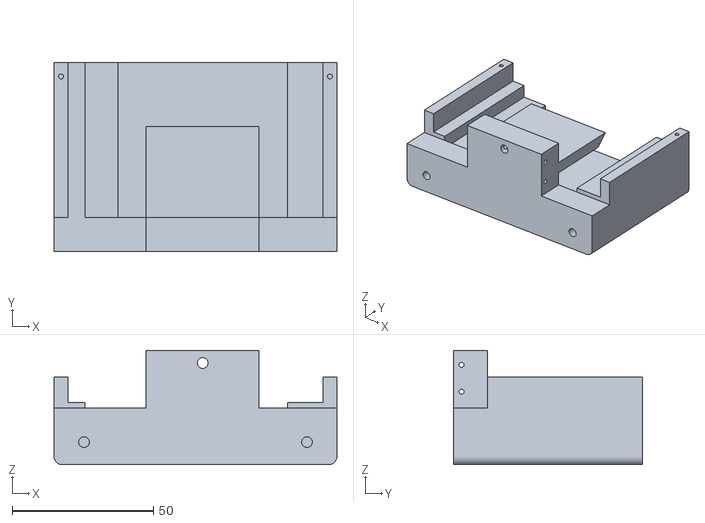
[picture p72: CAD file, 2022-05-03]
FreeCAD/tymkrs_Cyphercon_2020/Holder front (Meshed).stl
100.2 x 67.0 x 40.5
