Wireb/Cyphercon-5_3-2022/FreeCAD/tymkrs_Cyphercon_2020/starfish (Meshed).stl

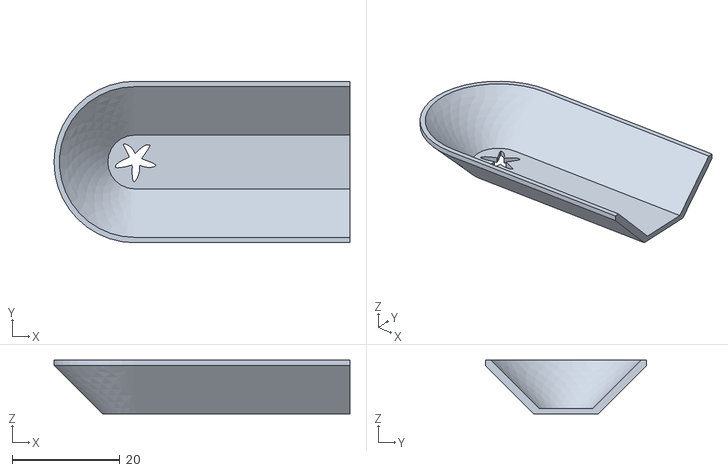
[picture p73: CAD file, 2022-05-03]
FreeCAD/tymkrs_Cyphercon_2020/starfish (Meshed).stl
55.0 x 30.0 x 10.0
